volab/IoT_EPS/_1_userDoc/source/volabid.rst

:Auteur: J.Soranzo
:Societe: `VoRoBoTics`_
:Entity: `VoLAB`_

.. _`VoLAB` : http://www.vorobotics.com/wp/

.. _`VoRoBoTics` : http://www.vorobotics.com/wp/
