volab/IoT_EPS/_1_userDoc/source/chronogram.rst

++++++++++++++++++++++++++++++++++++++++++++++++++++++++++++++++++++++++++++++++++++++++++++++++++++
IoTEps Chronogram
++++++++++++++++++++++++++++++++++++++++++++++++++++++++++++++++++++++++++++++++++++++++++++++++++++

:Auteur: J.Soranzo
:Date de création: 08/2021
:Last update: 08/2021
:Societe: VoRoBoTics
:Entity: VoLAB

.. contents::
    :backlinks: top

====================================================================================================
Oscilloscope readings: loop cycle study
====================================================================================================
This timing chronogram was made with a **special version of the firmaware** that use PB0(D6) of
the ESP8266 input redefined as output. 

Shortest loop cycle
----------------------------------------------------------------------------------------------------
  
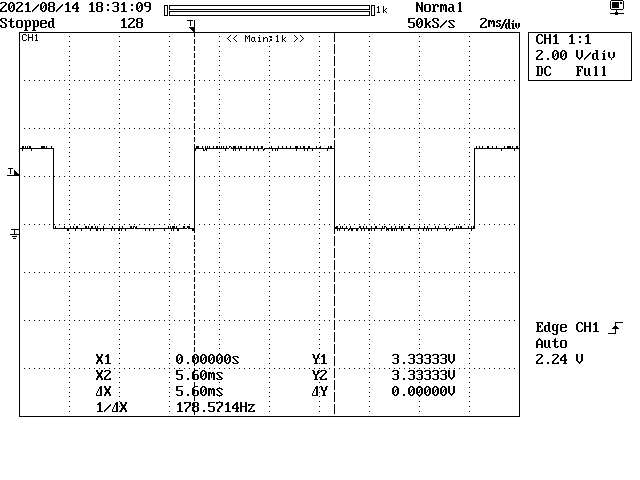
[picture p35: _1_userDoc/source/image/bestCycleTime5ms.JPG]


    Shortest loop cycle

The shortest loop cycle in idle stade is 5.6ms

A strange cycle
----------------------------------------------------------------------------------------------------

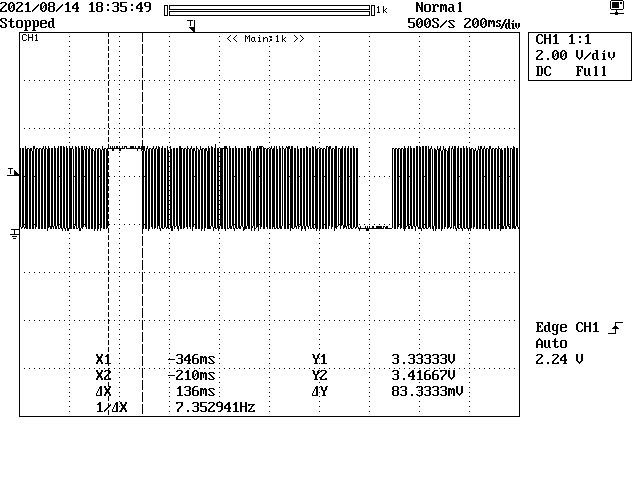
[picture p36: _1_userDoc/source/image/136msCycleEvery1s.JPG]


    136ms cycle every 1s
    
Probably web server check. Plug is in idle state (nothing to do). No 1s period timer in our code.

Push button cycle
----------------------------------------------------------------------------------------------------

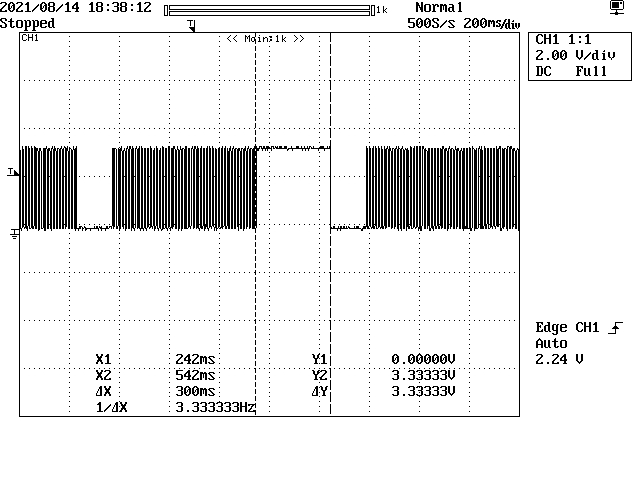
[picture p37: _1_userDoc/source/image/pushButon300msCycle.JPG]


    Handle a plug psuh button 

This operation take 300ms.

Plug on/off handler duration
----------------------------------------------------------------------------------------------------

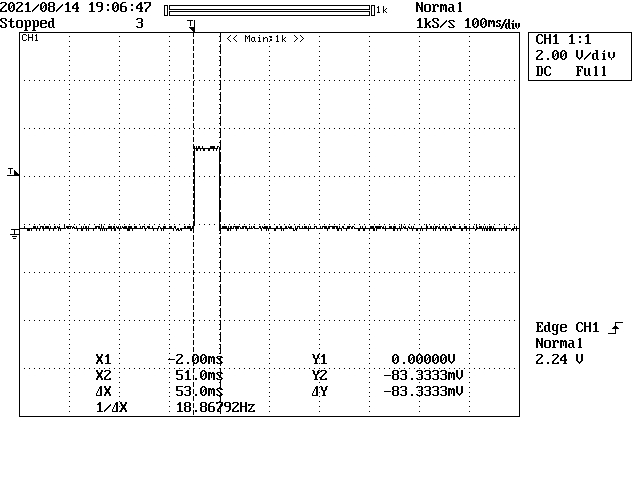
[picture p38: _1_userDoc/source/image/plugOnOff_53ms.JPG]


    Plug on/off handler take 53ms
    
and

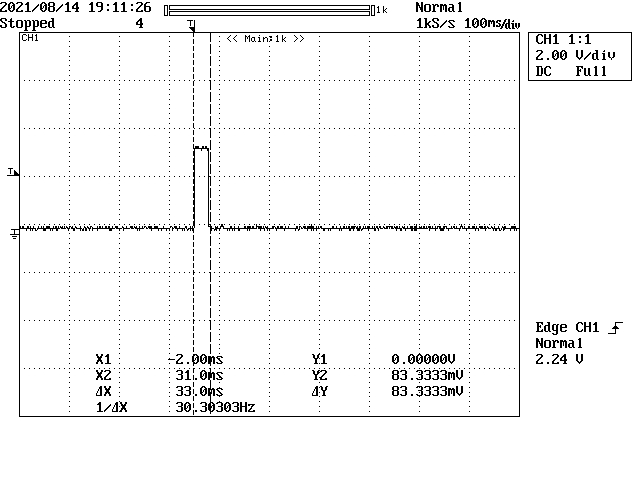
[picture p39: _1_userDoc/source/image/plugOnOff_33ms_withoutDebugPrints.JPG]


    Plug on off without debug prints 

Without debug prints on serial it take only 33ms.

A complete web exchange
----------------------------------------------------------------------------------------------------

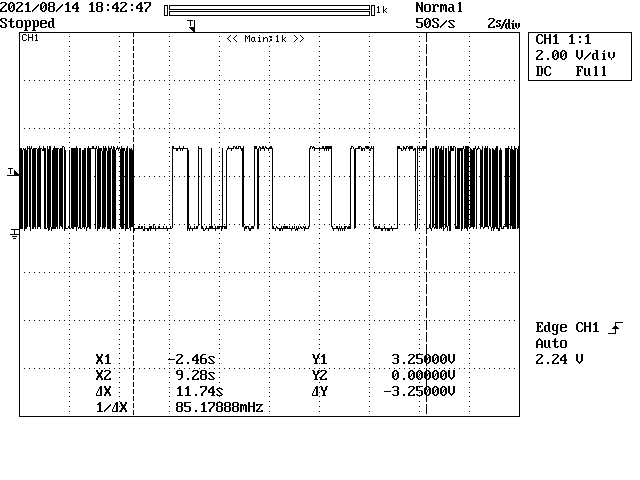
[picture p40: _1_userDoc/source/image/completeWebExchange.JPG]


    Complete web exchange : 11.74s (very long)

That correspond to::

    <Volab handleIndex > Mode Station index page
    handleFileRead: /
    handleFileRead _path : /index.html (48ko)
    handleFileRead _path : /css/sidebar.css (2ko)
    handleFileRead _path : /css/style.css (4ko)
    handleFileRead _path : /js/myLog.js (1k)
    handleFileRead _path : /js/regExPatern.js (9k)
    handleFileRead _path : /js/plug.js (19k)
    handleFileRead _path : /js/main.js (14k)
    handleFileRead _path : /js/table.js (9k)
    handleFileRead _path : /img/green.png (28k)
    handleFileRead _path : /img/logo_alpha.png (83k)
    handleFileRead _path : /img/red.png (28k)
    handleFileRead _path : /img/blue.png (28k)
    handleFileRead _path : /img/yellow.png (30k)
    handleFileRead _path : /config4.json (1.7k)

Only the function handlehtmlReq (tag pin toggle move in the function)

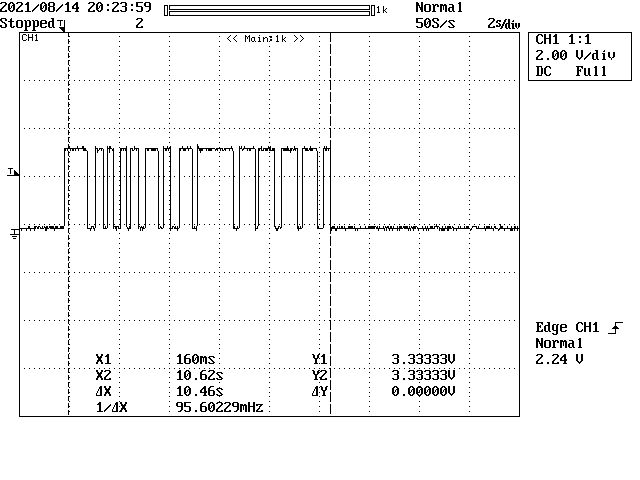
[picture p41: _1_userDoc/source/image/handleHtmlReqSlash.JPG]


    Juste time of the function 

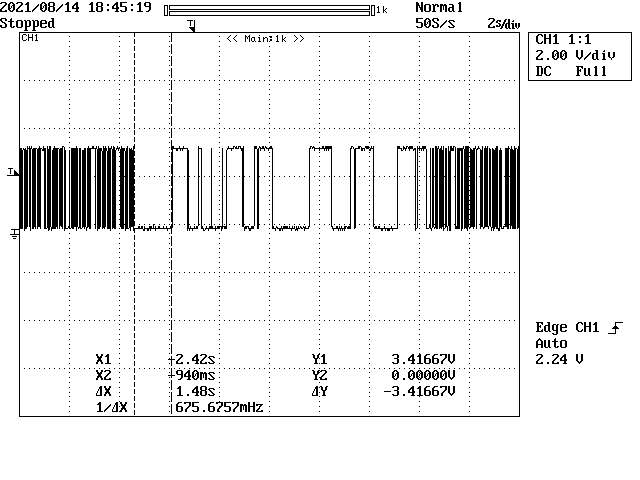
[picture p42: _1_userDoc/source/image/veryLongCycle1.48s.JPG]


    1.48s cyle

Probably the transfert of index.html

Handel html param in manual mode - example
----------------------------------------------------------------------------------------------------

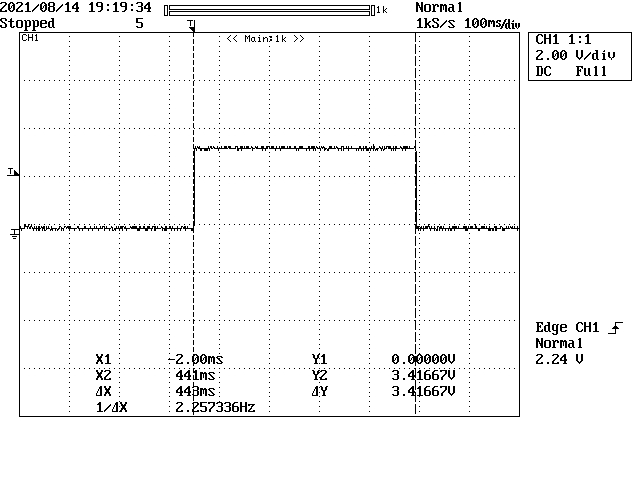
[picture p43: _1_userDoc/source/image/handleHtmlParamManualMode443ms.JPG]


    Web browser set one plug manual mode on or off
    
This operation take 443ms

====================================================================================================
Conclusions
====================================================================================================
Serial prints takes time !

The size of the files should be shorten (logo, green.png, yellow.png... javascript files)
