volab/IoT_EPS/_1_userDoc/source/pitch.rst

.. index::
    single: Pitch

++++++++++++++++++++++++++++++++++++++++++++++++++++++++++++++++
IOT Electrical Power strip from VoLAB
++++++++++++++++++++++++++++++++++++++++++++++++++++++++++++++++

.. contents:: Table of Contents
    :backlinks: top

====================
Pitcher
====================

Séléectionner ses susjets

Les tiroirs : indispensables et secondaire

CONVAINCRE

Qu'est'est-ce que je fais là ?

Qu'est-ce qu'ils font là ?

Gagner quoi ?

Se connecter à son auditoire

pas de jargon pas d'acronyme, visualisable

La lecture du non-verbal

====================
Winning Pitch
====================

Why 
----------------------------------------------------------------------------------------------------
#. aspirationnel
#. quantitatif

What
----------------------------------------------------------------------------------------------------
#. what extérieur : nom du projet, ce qu'il fait ou va faire
#. what intérieur : proposition de b=valeur innovante

Attention à la définition de innovant ne veut pas dire nouveau

Who
----------------------------------------------------------------------------------------------------
#. Par qui est porté
#. pour qui

Ci-dessus : le Warm-up pour créer l'envie

Projection pour créer l'adhésion
----------------------------------------------------------------------------------------------------

Projeter son auditoire dans l'utilisation du projet (vendre du rêve)

====================
IoT EPS
====================

Prise multiple connectée

Pourquoi ? : besoins

Cycle de croissance des plantes

Gestion de l'éclairage jour/nuit d'un aquarium

Simple minuteur

Gestion de l'éclairage quand on est en vacance

Arroser les plantes périodiqement

Pourquoi quantitatif

objectif moins de 50€

10A / prise soit 2400W avec un limite totale cumulée de 3840W

Fabricable par n'importe qui en moins de 3 heures

Quoi
 
IoT EPS Electrical Power Plug

Prise multiple connecté 4 voies avec minuteur incorporé
et mesure individuelle de puissance  pour chaque voie

Projet DiY, connecté (en Wifi)

pas d'application dédiée.

Accessible par navigateur internet

Point d'accès ou mode client Wifi

Qui

Porté par le VoLAB fabLab de Vauréal

Réalisable par tous.

Sources (électroniques, logiciels et mécaniques) disponibles sur le site internet

Se projecter

Accessible à tous.

Simple d'utilisation

Bouton mécanique pour garder la main
