volab/IoT_EPS/_1_userDoc/infography/01_Screen.jpg

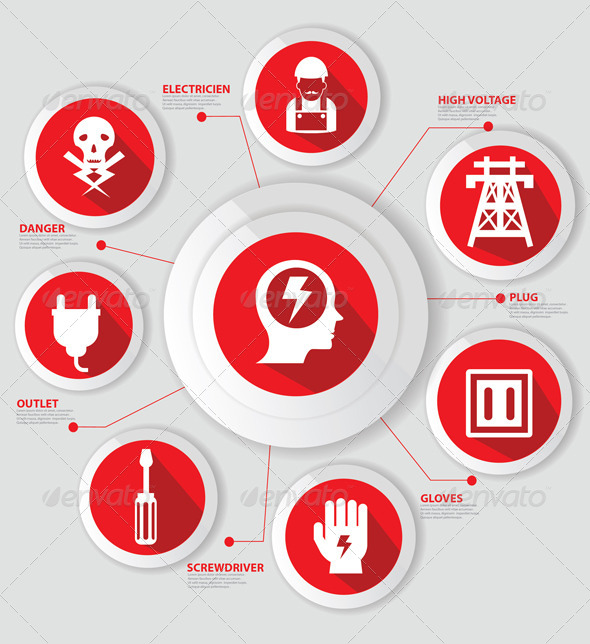
_1_userDoc/infography/01_Screen.jpg
