volab/IoT_EPS/_1_userDoc/infography/il_794xN.2478645642_a8mu.webp

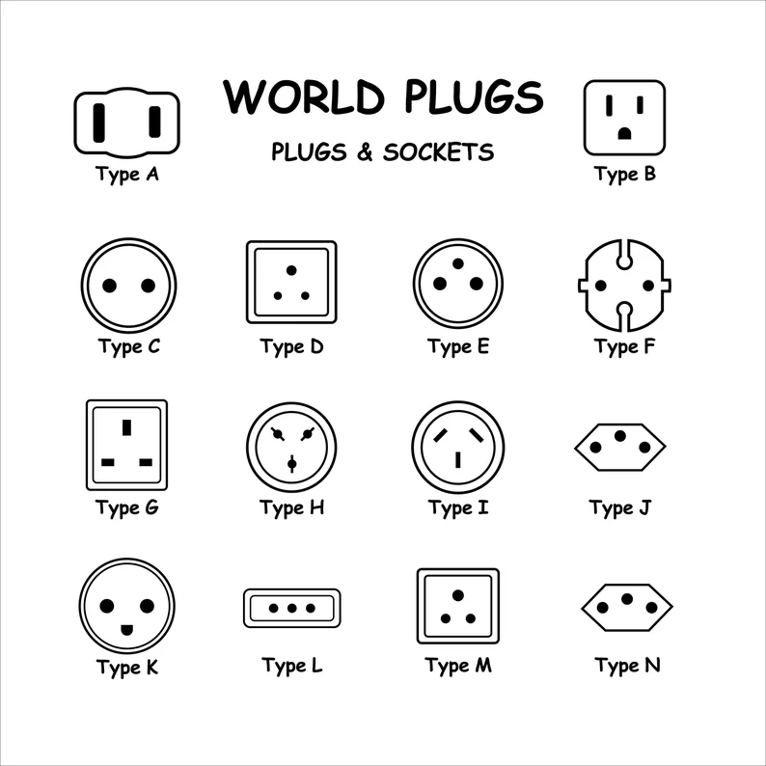
_1_userDoc/infography/il_794xN.2478645642_a8mu.webp
