volab/IoT_EPS/_1_userDoc/source/image/ACS712goodModul.jpg

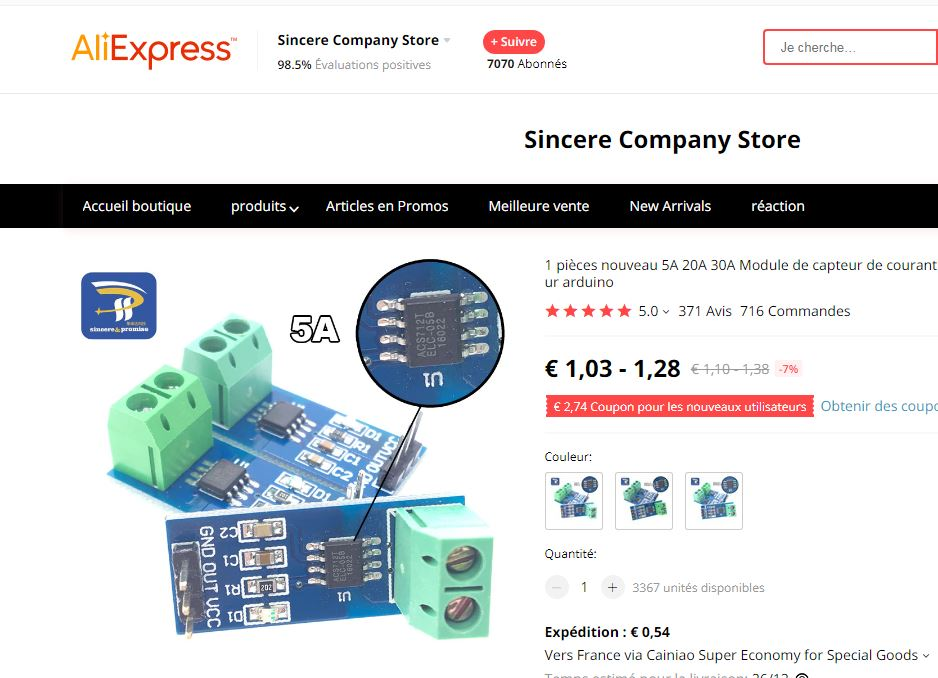
_1_userDoc/source/image/ACS712goodModul.jpg
