volab/IoT_EPS/_1_userDoc/source/image/TPLink_20200208_150122.jpg

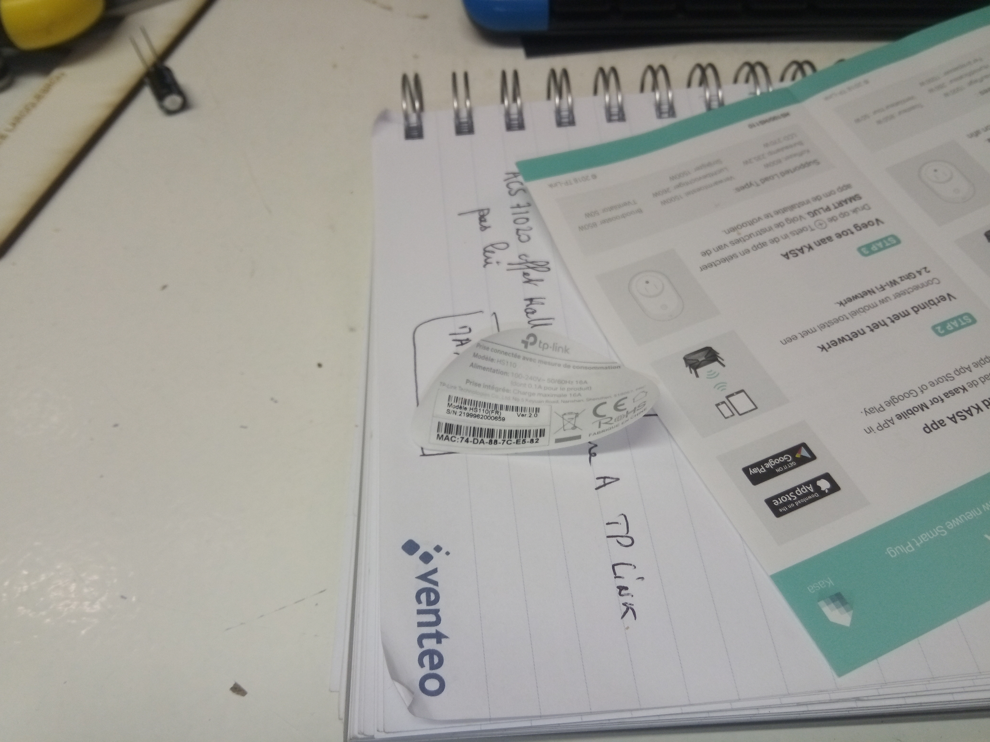
_1_userDoc/source/image/TPLink_20200208_150122.jpg
