volab/IoT_EPS/_3_software/IoT_EPS/data/img/blue.png

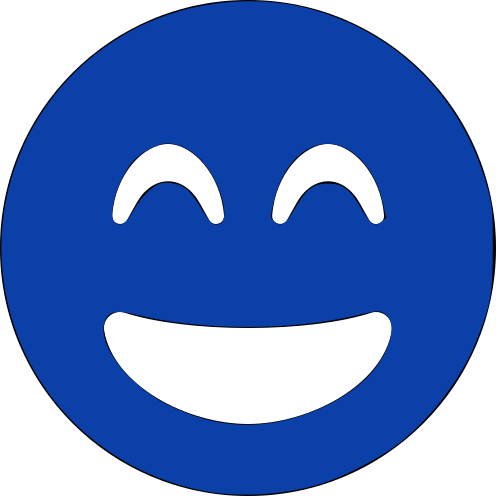
_3_software/IoT_EPS/data/img/blue.png
