volab/IoT_EPS/_3_software/IoT_EPS/data/img/yellow.png

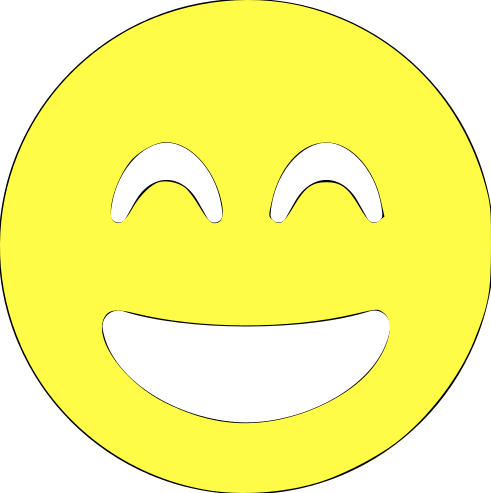
_3_software/IoT_EPS/data/img/yellow.png
