volab/IoT_EPS/_3_software/pythonTools/images/guiCalMag.JPG

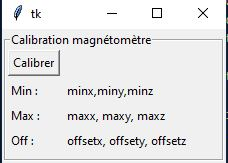
_3_software/pythonTools/images/guiCalMag.JPG
