volab/IoT_EPS/_3_software/pythonTools/images/guiDisplays.JPG

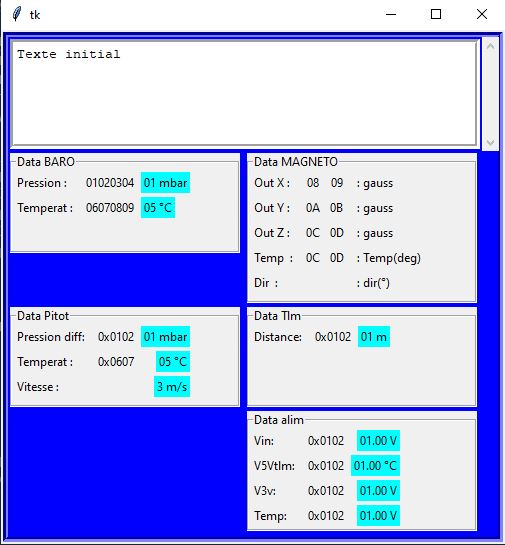
_3_software/pythonTools/images/guiDisplays.JPG
