volab/IoT_EPS/_3_software/pythonTools/images/guiRecord.JPG

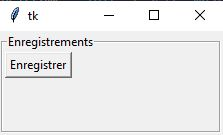
_3_software/pythonTools/images/guiRecord.JPG
