volab/IoT_EPS/_3_software/pythonTools/pytemplt/doc/images/ihm.jpg

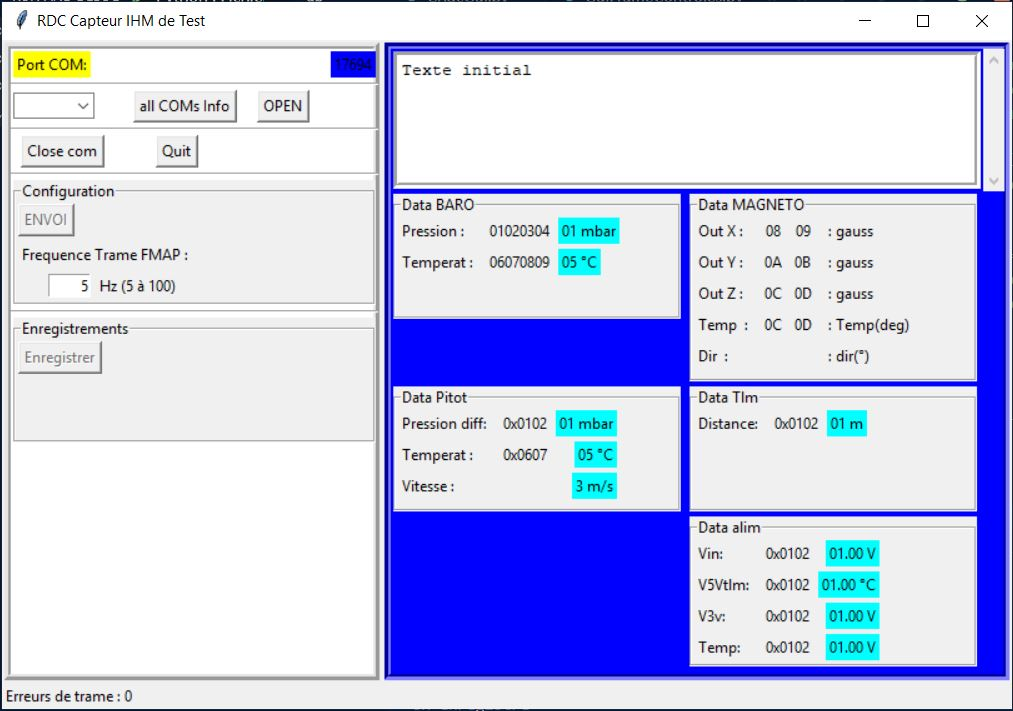
_3_software/pythonTools/pytemplt/doc/images/ihm.jpg
