volab/IoT_EPS/_1_userDoc/infography/ultimate-guide-to-travel-plugs.jpg

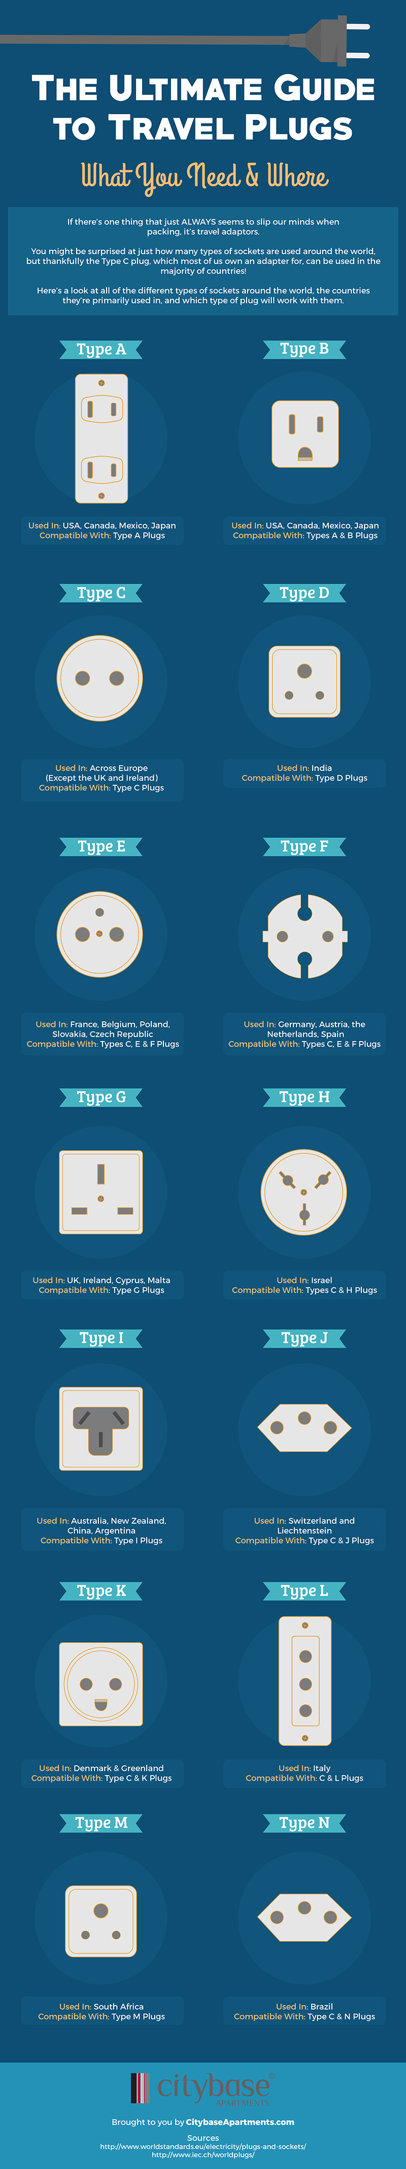
_1_userDoc/infography/ultimate-guide-to-travel-plugs.jpg
