volab/IoT_EPS/_4_PCB/IOTESP_PowerPlug_v1/IOTESP_PowerPlugv1.sch

## KiCad design _4_PCB/IOTESP_PowerPlug_v1/IOTESP_PowerPlugv1.sch (2019-04-12)

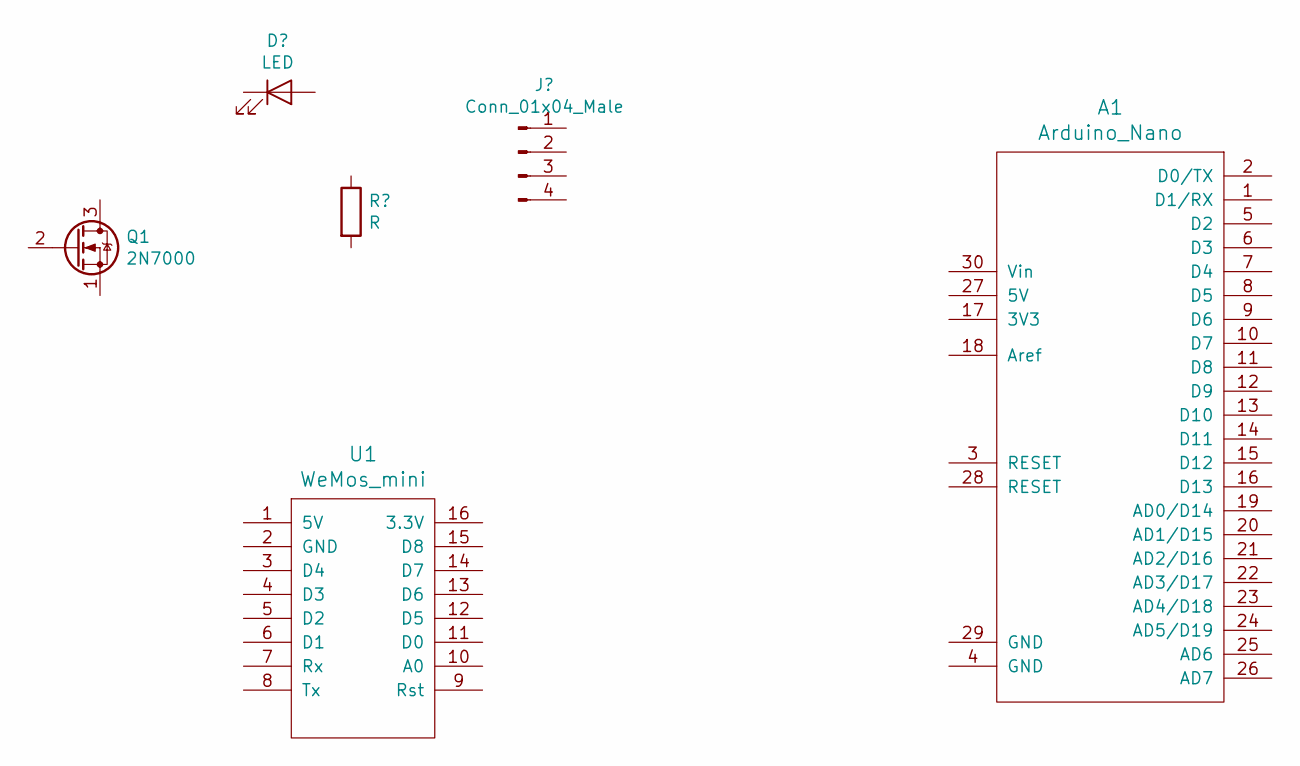
[picture p84: schematic IOTESP_PowerPlugv1.sch]

Parts:
A1: Arduino_Nano; arduino_nano
Q1: 2N7000; TO-92_Inline_Narrow_Oval
U1: WeMos_mini; D1_mini_board
