volab/IoT_EPS/_3_software/IoT_EPS/jsonIotEps.cpp

/**
* @file cpowerplug.cpp
* @author J.Soranzo
* @date 10/11/2018
* @copyright see project readme 
* @version 1.0
* @brief This class is the plug class for Electrical Power Strip project
*/

#include "jsonIotEps.h"

bool CJsonIotEps::init( ConfigParam *pcParam, CPowerPlug *plugs){
    _pcParam = pcParam;
    _pPlugs = plugs;
    return true;
}


/**
 @fn bool CJsonIotEps::checkIfStoreNeeded()
 @brief Check if CParam or CPowerPlugs store json file is needed
 @return true if store is needed
*/
bool CJsonIotEps::checkIfStoreNeeded(){
    bool retVal = false;
    DEFDPROMPT("JsonIotEps");
    
    if ( _pcParam->_jsonWriteRequest ){
        retVal=true;
    } else { //if true no need to test plug causeonly one json file
        for (int i = 0; i < _pcParam->getNumberOfPlugs(); i++ ){
            retVal |= _pPlugs[i]._jsonWriteRequest;
            //_pPlugs[i]._jsonWriteRequest = false; //to be remove after test
        }
    }

    return retVal;
}



/**
 @fn void CJsonIotEps::printFileIntegrity()
 @brief Print file integrity for debug purpose
 @return no param and no return
*/
void CJsonIotEps::printFileIntegrity(){
    DEFDPROMPT("Json file integrity print function");

    switch (_jsonFileIntegrity){
        case KEEP_MASTER:
            DSPL( dPrompt + F("Keep master"));
            //_fileNameToLoad = CONFIGFILENAME;
            break;
        case KEEP_COPY1:
            DSPL( dPrompt + F("Keep copy 1"));
            //_fileNameToLoad = CONFIGFILENAME_COPY1;
            break;  
        case KEEP_COPY2:
            DSPL( dPrompt + F("Keep copy 1"));
            //_fileNameToLoad = CONFIGFILENAME;
            break;
        case FILES_ERROR:
            DSPL( dPrompt + F("Fatal file error"));
            //_fileNameToLoad = "";
            break;           
        default:
            break;
    }
}

bool CJsonIotEps::storeJson(){
    DEFDPROMPT( "CJsonIotEps store json method" );
    DSPL( dPrompt + F("*********JSON WRITE REQUESTED***************"));
    bool retVal = false;
    

//What is the logic ?
//What is the one that this the more efficient ?
// 3 succesives writes
// followed by 3 checks and if there is error we restart x times

//from softdev.rst REX:
//Finally we decide to write only 2 files and keep the third as a template to restaure a default
//situation if the 2 others files are corrupts. This Third file is only writes when the user
//change the configuration.

//try to write conf1: _checkJsonOneFileIntegrity file1
// if ok : 
    // first write
    DSPL( dPrompt + F("Master json file write") );
    if ( _checkJsonOneFileIntegrity( CONFIGFILENAME ) ){
        _storeOneJsonFile( CONFIGFILENAME, CONFIGFILENAME );
        DSPL( dPrompt + F("store master config file with himself as model"));
        retVal = true;
    } else if ( _checkJsonOneFileIntegrity( CONFIGFILENAME_COPY1 )) {
        _storeOneJsonFile( CONFIGFILENAME_COPY1, CONFIGFILENAME );
        DSPL( dPrompt + F("store master config file with copy1 as model"));
        /** @todo [NECESSARY] rise error write config file 1 */
        retVal = true;
    } else if ( _checkJsonOneFileIntegrity( CONFIGFILENAME_COPY2 )) {
        _storeOneJsonFile( CONFIGFILENAME_COPY2, CONFIGFILENAME );
        DSPL( dPrompt + F("store master config file with copy2 as model"));
        /** @todo [NECESSARY] rise error write config file 1 with rescue values*/
        retVal = true; // or false ??? the plugs value maybe not up todate
    } else {
        /** @todo [NECESSARY] rise fatal error write config file 1 */
    }

    //second write
    DSPL( dPrompt + F("Copy 1 Json file write") );
    if ( _checkJsonOneFileIntegrity( CONFIGFILENAME ) ){
        _storeOneJsonFile( CONFIGFILENAME, CONFIGFILENAME_COPY1 );
        DSPL( dPrompt + F("store config file copy 1 with master as model"));
    } else if ( _checkJsonOneFileIntegrity( CONFIGFILENAME_COPY1 )) {
        _storeOneJsonFile( CONFIGFILENAME_COPY1, CONFIGFILENAME_COPY1 );
        DSPL( dPrompt + F("store config file copy 1 with himself as model"));
        //not an error
    } else if ( _checkJsonOneFileIntegrity( CONFIGFILENAME_COPY2 )) {
        _storeOneJsonFile( CONFIGFILENAME_COPY2, CONFIGFILENAME_COPY1 );
        DSPL( dPrompt + F("store config file copy 1 with copy 2 as model"));
    } else {
        /** @todo [NECESSARY] rise low error write config file 2 */
    }

    //third write only when config paramters has changed
    if ( _pcParam->_jsonWriteRequest ){
        if ( _checkJsonOneFileIntegrity( CONFIGFILENAME ) ){
            _storeOneJsonFile( CONFIGFILENAME, CONFIGFILENAME_COPY2 );
            DSPL( dPrompt + F("store config file copy 2 with master as model"));
        } else if ( _checkJsonOneFileIntegrity( CONFIGFILENAME_COPY1 )) {
            _storeOneJsonFile( CONFIGFILENAME_COPY1, CONFIGFILENAME_COPY2 );
            DSPL( dPrompt + F("store config file copy 2 with copy 1 as model"));
            //not an error
        } else if ( _checkJsonOneFileIntegrity( CONFIGFILENAME_COPY2 )) {
            _storeOneJsonFile( CONFIGFILENAME_COPY2, CONFIGFILENAME_COPY2 );
            DSPL( dPrompt + F("store config file copy 2 with himself as model"));
        } else {
            /** @todo [NECESSARY] rise low error write config file 3 */
        }
    }

    //clear json write request
    if ( retVal ){
        _pcParam->_jsonWriteRequest = false;
        for (int i = 0; i < _pcParam->getNumberOfPlugs(); i++ ){
            _pPlugs[i]._jsonWriteRequest = false;
        }
        _retryStoreCpt = 0;
    } else if (_retryStoreCpt < 4 ){ // next retry at next main loop
        _retryStoreCpt++;
    } else {
        /** @todo rise fatal error 3 retry on store config files */
    }

    return retVal;
}

void CJsonIotEps::_storeOneJsonFile(String file_name_model, String file_name_to_store){

    DEFDPROMPT( "CJsonIotEps store one json method" );

    File configFile = SPIFFS.open( file_name_model , "r");
    DSPL( dPrompt + "file = "+ file_name_to_store + " with model = " + file_name_model);
    if (configFile) {
        size_t size = configFile.size();
        // Allocate a buffer to store contents of the file.
        std::unique_ptr<char[]> buf(new char[size]);
        configFile.readBytes(buf.get(), size);
        configFile.close();
        DSPL( dPrompt + F("Config File loaded") );
        DynamicJsonBuffer jsonBuffer;
        JsonObject& json = jsonBuffer.parseObject(buf.get());
        if (json.success()) {
            DSPL( dPrompt + F("populate json general parm") );
            json["general"]["softAP_IP"] = _pcParam->_addIP.toString( );
            json["general"]["numberOfPlugs"] = String( _pcParam->_numberOfPlugs );
            json["general"]["softAP_port"] = String( _pcParam->_serverPort );
            json["general"]["startInAPMode"] = (_pcParam->_wifimode == "softAP") ? "ON":"OFF";
            if ( _pcParam->_firstBoot == ConfigParam::YES ){
                json["general"]["firstBoot"] = "ON";
            } else if( _pcParam->_firstBoot == ConfigParam::NO ){
                json["general"]["firstBoot"] = "OFF";
            } else { // ConfigParam::TRY
                json["general"]["firstBoot"] = "TRYSTA";
            }
            json["general"]["STAmaxWifiConnectionRetry"] = String( _pcParam->_STAmaxWifiConnectionRetries );
            json["general"]["hostName"] = _pcParam->_host;
            json["general"]["allLedsOnTime"] = String(_pcParam->_allLedsOnTime);
            json["general"]["ledsGlobalLuminosity"] = String( _pcParam->_ledsGlobalLuminosity );
            json["general"]["powerLedEconomyMode"] = _pcParam->_powerLedEconomyMode?"ON":"OFF";
            json["general"]["macAdd"] = String( _pcParam->_macAdd );
            json["general"]["softAP_macAdd"] = String( _pcParam->_softAPMacAdd );
            json["general"]["dhcp_mode"] = _pcParam->_DHCPMode?"ON":"OFF";
            json["general"]["staIP"] = _pcParam->_staIP.toString();
            json["general"]["staGateway"] = _pcParam->_staGateway.toString( );
            json["general"]["emplacement"] = String( _pcParam->_emplacement );
            for (int i = 0; i < _pcParam->getNumberOfPlugs(); i++ ){
                JsonObject& plug = json[_pPlugs[i].getPlugName()];
                DSPL( dPrompt + _pPlugs[i].getPlugName() + " write req = " + _pPlugs[i]._jsonWriteRequest );
                plug["nickName"] = _pPlugs[i]._nickName;
            }

            for (int i = 0; i < _pcParam->getNumberOfPlugs(); i++ ){
                if ( _pPlugs[i]._jsonWriteRequest ){
                    JsonObject& plug = json[_pPlugs[i].getPlugName()];
                    DSPL( dPrompt + F("plug to be writed : ") + _pPlugs[i].getPlugName() );
                    plug["State"] = _pPlugs[i]._state?"ON":"OFF";
                    plug[JSON_PARAMNAME_PAUSE] = _pPlugs[i]._pause?"ON":"OFF";
                    plug["Mode"] = _pPlugs[i].getStringMode();
                    plug["hDebut"] = _pPlugs[i]._hDebut.getStringVal();
                    plug["hFin"] =  _pPlugs[i]._hFin.getStringVal();
                    plug["dureeOn"] = _pPlugs[i]._dureeOn.getStringVal();
                    plug["dureeOff"] = _pPlugs[i]._dureeOff.getStringVal();
                    plug["clonedPlug"] = _pPlugs[i]._clonedPlug;
                    plug["onOffCount"] = String(_pPlugs[i]._onOffCount);
                    // plug["onOffCount"] = String(0);
                    plug[JSON_PARAMNAME_NEXTSWITCH] = String(_pPlugs[i]._nextTimeToSwitch);

                    //Special for day of week
                    JsonArray& plugJours = plug["Jours"];
                    for (int j = 0; j<7; j++){ //7 bits for 7 days
                        if ( bitRead( _pPlugs[i]._daysOnWeek, j ) ) plugJours[ j ]="ON";
                        else plugJours[ j ] = "OFF";
                        String jourEtat = plugJours[ j ];
                        DSPL(dPrompt + F("Jour : ") + String(j) + " = " + jourEtat );
                    }  
                }
            }
            configFile = SPIFFS.open( file_name_to_store , "w");
            json.printTo(configFile);

        } else {
            DEBUGPORT.println(dPrompt + F("Failed to load json config"));
            // return false;
        }
        //configFile.close();
        // return true;        
    }
}

/**
 @fn bool CJsonIotEps::loadJsonPlugParam( int plugNumber, int mainPowerSwitchState )
 @brief Check the integrity of json file
 @param plugNumber : Number of plugs in the system
 @param mainPowerSwitchState : to decide if we stat normaly or if we need to stop all plugs.
 @return a booleen true if all is ok.

 Need the integrity is checked before use it
*/
bool CJsonIotEps::loadJsonPlugParam( int plugNumber, int mainPowerSwitchState ){
    bool returnVal = false;
    String sState, sMode, sHDebut, sHFin, sDureeOn, sDureeOff;
    String sClonedPlug, sOnOffCount, sNextTime2switch, sPause;
    String sNickName;
    String sJours[7];
    bool writeReq = false;

    DEFDPROMPT( "Load Json Plugs Data");
    DSPL( dPrompt + F("Enter in the fonction. ")  );
    if ( _jsonFileIntegrity != FILES_ERROR ){
        File file = SPIFFS.open( _fileNameToLoad, "r");
        DSPL( dPrompt + F("File open ") + _fileNameToLoad );
        if (file){
            size_t size = file.size();
            std::unique_ptr<char[]> buf(new char[size]);
            file.readBytes(buf.get(), size);
            file.close();
            DynamicJsonBuffer jsonBuffer;
            JsonObject& json = jsonBuffer.parseObject(buf.get());
            if (json.success()){
                for (int i = 0; i < plugNumber; i++ ){
                    JsonObject& plug = json[_pPlugs[i].getPlugName()]; // bug on/off count 15/01/2022
                    if ( mainPowerSwitchState == 1 ){ // 1 if switch is on
                        // JsonObject& plug = json[_pPlugs[i].getPlugName()];
                        sNickName = plug["nickName"].as<String>();
                        sState = plug["State"].as<String>();
                        sPause = plug[JSON_PARAMNAME_PAUSE].as<String>();
                        sMode = plug["Mode"].as<String>();
                        sHDebut = plug["hDebut"].as<String>();
                        sHFin = plug["hFin"].as<String>();
                        sDureeOn = plug["dureeOn"].as<String>();
                        sDureeOff = plug["dureeOff"].as<String>();
                        sClonedPlug = plug["clonedPlug"].as<String>();
                        sOnOffCount = plug["onOffCount"].as<String>();
                        sNextTime2switch = plug[JSON_PARAMNAME_NEXTSWITCH].as<String>();

                        

                        DSPL( dPrompt + F("Plug name : ") + _pPlugs[i].getPlugName() );
                        DSPL( dPrompt + F("Nick name : ") + sNickName );
                        DSPL( dPrompt + F("Etat = ") + sState );
                        DSPL( dPrompt + F("Pause state = ") + sPause );
                        DSPL( dPrompt + F("Mode = ") + sMode );
                        DSPL( dPrompt + F("Start time = ") + sHDebut );
                        DSPL( dPrompt + F("End time = ") + sHFin );
                        DSPL( dPrompt + F("on duration = ") + sDureeOn );
                        DSPL( dPrompt + F("off duration = ") + sDureeOff );
                        DSPL( dPrompt + F("Cloned plug = ") + sClonedPlug );
                        DSPL( dPrompt + F("Relay on off count = ") + sOnOffCount );
                        DSPL( dPrompt + F("next time to switch = ") + sNextTime2switch );
                        /////////////////////////////////////////////////////////////////////////////
                        //    plugs member updates                                                 //
                        /////////////////////////////////////////////////////////////////////////////
                        _pPlugs[i]._nickName = sNickName;
                        _pPlugs[i]._state = (sState == "ON");
                        _pPlugs[i]._pause = ( sPause == "ON" );
                        _pPlugs[i]._mode = _pPlugs[i].modeId( sMode ); 
                        _pPlugs[i]._hDebut = CEpsStrTime( sHDebut, CEpsStrTime::HHMM);
                        _pPlugs[i]._hFin = CEpsStrTime( sHFin, CEpsStrTime::HHMM );
                        _pPlugs[i]._dureeOn = CEpsStrTime( sDureeOn, CEpsStrTime::MMM );
                        _pPlugs[i]._dureeOff = CEpsStrTime( sDureeOff, CEpsStrTime::MMM );
                        _pPlugs[i]._clonedPlug = sClonedPlug;
                        _pPlugs[i]._onOffCount = sOnOffCount.toInt();
                        _pPlugs[i]._nextTimeToSwitch = sNextTime2switch.toInt();

                        //restaure physical state of the plug
                        // 8/01/2022
                        // from CPowerPlug::readFromJson line 222
                        if ( _pPlugs[i]._state && (!_pPlugs[i]._pause) ) _pPlugs[i].on(); else _pPlugs[i].off();
                        
                        /////////////////////////////////////////////////////////////////////////////
                        //    special for days of Hebdo mode                                       //
                        /////////////////////////////////////////////////////////////////////////////
                        DSPL( dPrompt + "Jours : ");
                        JsonArray& plugJours = plug["Jours"];
                        _pPlugs[i]._daysOnWeek = 0;
                        for ( int i = 0; i < 7 ; i++ ){
                            sJours[i] = plugJours[i].as<String>();
                            // DSPL( dPrompt + "jours " + (String)i + " = " + sJours[i] );
                            if (sJours[i] == "ON"){
                                DSPL( "Jours " + (String)i + " est ON. " );
                                bitSet( _pPlugs[i]._daysOnWeek, i);
                            } else {
                                DSPL( "Jours " + (String)i + " est OFF. " );
                            } 
                        }
                        DSPL("");                        
                    } else { // main power switch is off stop all plugs
                    //plugs return to manual mode OFF state.
                        sOnOffCount = plug["onOffCount"].as<String>();
                        _pPlugs[i]._onOffCount = sOnOffCount.toInt(); // bug on/off count 15/01/2022
                        _pPlugs[i].handleBpLongClic();
                        writeReq = writeReq | _pPlugs[i]._jsonWriteRequest;
                        _pPlugs[i]._jsonWriteRequest = false;
                    }
                }
            }
            if ( writeReq ){
                storeJson();
            }
            returnVal = true;
        }

    } else {
        DSPL( dPrompt + F("Json file integrity error") );
    }


    return (returnVal);
}

/**
 @fn bool CJsonIotEps::loadJsonConfigParam()
 @brief Check the integrity of json file
 @return a booleen true if all is ok.

 Need the integrity is checked before use it
*/
bool CJsonIotEps::loadJsonConfigParam(){
    //bool _fileLoaded = false;
    DEFDPROMPT("CJson Config Param Loading")
    bool returnVal = false;

    if ( _jsonFileIntegrity != FILES_ERROR ){
        File file = SPIFFS.open( _fileNameToLoad, "r");
        if (file){
            size_t size = file.size();
            std::unique_ptr<char[]> buf(new char[size]);
            file.readBytes(buf.get(), size);
            file.close();
            DynamicJsonBuffer jsonBuffer;
            JsonObject& json = jsonBuffer.parseObject(buf.get());
            if (json.success()){
                String s_IpAdd = json["general"]["softAP_IP"].as<String>();
                _pcParam->_addIP.fromString( s_IpAdd );
                _pcParam->_numberOfPlugs = json["general"]["numberOfPlugs"].as<String>().toInt();
                _pcParam->_serverPort = json["general"]["softAP_port"].as<String>().toInt();
                String startInAPMode = json["general"]["startInAPMode"].as<String>();
                if ( startInAPMode == "OFF") _pcParam->_wifimode = "Station";
                else _pcParam->_wifimode = "softAP";
                String s_FirstBootTmp = json["general"]["firstBoot"].as<String>();
                //possible value are "ON" "OFF" or "TRYSTA"
                if ( s_FirstBootTmp == "ON") _pcParam->_firstBoot = ConfigParam::YES;
                else if ( s_FirstBootTmp == "OFF" ) _pcParam->_firstBoot = ConfigParam::NO;
                else if ( s_FirstBootTmp == "TRYSTA" ) _pcParam->_firstBoot = ConfigParam::TRY;
                else _pcParam->_firstBoot = ConfigParam::YES; // default value
                _pcParam->_STAmaxWifiConnectionRetries = \
                        json["general"]["STAmaxWifiConnectionRetry"].as<String>().toInt();
                _pcParam->_host = json["general"]["hostName"].as<String>();
                _pcParam->_allLedsOnTime = json["general"]["allLedsOnTime"].as<String>().toInt();
                _pcParam->_ledsGlobalLuminosity = \
                    json["general"]["ledsGlobalLuminosity"].as<String>().toInt();
                _pcParam->_powerLedEconomyMode = \
                        (json["general"]["powerLedEconomyMode"].as<String>() == "ON");
                _pcParam->_macAdd = json["general"]["macAdd"].as<String>();
                _pcParam->_softAPMacAdd = json["general"]["softAP_macAdd"].as<String>();
                _pcParam->_DHCPMode = ( json["general"]["dhcp_mode"].as<String>() == "ON" );
                String s_tmpIP = json["general"]["staIP"].as<String>();
                _pcParam->_staIP.fromString( s_tmpIP );
                s_tmpIP = json["general"]["staGateway"].as<String>();
                _pcParam->_staGateway.fromString( s_tmpIP );
                if (_pcParam->_firstBoot == ConfigParam::YES ) _pcParam->_wifimode = "softAP";
                _pcParam->_emplacement = json["general"]["emplacement"].as<String>();
                returnVal = true;
                /** @todo [NECESSARY] clear usage of NTP error */ 
            } else {
                DSPL(dPrompt + F("Failed to load json config"));     
                returnVal = false;
            }  
        }
        DSPL( dPrompt + F("Config param loaded : "));
        DSPL( dPrompt + F(" - emplacement : ") + _pcParam->_emplacement );
        DSPL( dPrompt + F(" - Number of plugs : ") + String(_pcParam->_numberOfPlugs) );
        DSPL( dPrompt + F(" - All Led On Time : ") + String(_pcParam->_allLedsOnTime)  );
        DSPL( dPrompt + F(" - LEDs Global illum : ") + String(_pcParam->_ledsGlobalLuminosity) );
        DSPL( dPrompt + F(" - Power Led economy mode : ") +  _pcParam->_powerLedEconomyMode );
        String firstBoot_s;
        switch (_pcParam->_firstBoot){
            case ConfigParam::YES:
                firstBoot_s = "YES";
                break;
            case ConfigParam::NO:
                firstBoot_s = "NO";
                break;
            case ConfigParam::TRY:
                firstBoot_s = "TRY";
                break;            
            default:
                break;
        }
        DSPL( dPrompt + F(" - First boot : ") +  firstBoot_s );
        DSPL( dPrompt + F(" - Host name : ") +  _pcParam->_host );
        DSPL( dPrompt + F(" - Strat in AP mode (_wifiMode) : ") + _pcParam->_wifimode  );
        DSP( dPrompt + F(" - Soft AP IP add (_addIP) : " )); _pcParam->_addIP.printTo(Serial);DSPL();
        DSPL( dPrompt + F(" - Soft AP port (_serverPort): ") + String(_pcParam->_serverPort)  );
        DSPL( dPrompt + F(" - DHCP mode  : ") + (_pcParam->_DHCPMode?"ON":"OFF")  );
        DSP( dPrompt + F(" - Station IP address  : ") );_pcParam->_staIP.printTo(Serial);DSPL();
        DSP( dPrompt + F(" - Station gateway IP address  : ") ); _pcParam->_staGateway.printTo(Serial);DSPL();
        DSPL( dPrompt + F(" - MAC address  : ") +  _pcParam->_macAdd  );
        DSPL( dPrompt + F(" - Soft AP MAC address  : ") + _pcParam->_softAPMacAdd  );
        DSPL( dPrompt + F(" - MAX Wifi connexion retry  : ") + String(_pcParam->_STAmaxWifiConnectionRetries)  );
        //DSPL( dPrompt + F(" - TNP Error  : ") +   ); //CSysSattus::ntpErr
    }
 
    return returnVal;
}

/**
 @fn CJsonIotEps::jsonFileIntegrity_t CJsonIotEps::checkJsonFilesIntegrity()
 @brief Check the integrity of json files
 @return jsonFileIntegrity Value.

 This method is called in the system init. It sets the _jsonFileIntegrity and 
 _fileNameToLoad private members.
*/
CJsonIotEps::jsonFileIntegrity_t CJsonIotEps::checkJsonFilesIntegrity(){ 
    // uint32_t H0 = 0;
    // uint32_t H1 = 0;
    // uint32_t H2 = 0;
    _jsonFileIntegrity = FILES_ERROR;

    DEFDPROMPT("Check Json Integrity")
/*
    DSPL( dPrompt +F("Mounting FS..."));
    ///SPIFFS Opning
    if (SPIFFS.begin()) {
        DSPL(dPrompt + F("File system mounted "));
        // if (SPIFFS.exists("/config.json")) {
        if (SPIFFS.exists( CONFIGFILENAME)) {
            //file exists, reading and loading
            DSPL(dPrompt + F("reading Json file master"));
            File configFile = SPIFFS.open( CONFIGFILENAME, "r");
            if (configFile) { H0 = _hashFile( configFile ); }
            DSPL(dPrompt + "H0 = " + String(H0));
        }
        if (SPIFFS.exists( CONFIGFILENAME_COPY1 )) {
            DSPL(dPrompt + F("reading Json file copy1"));
            File configFile = SPIFFS.open( CONFIGFILENAME_COPY1, "r");
            if (configFile) { H1 = _hashFile( configFile ); }
            DSPL(dPrompt + "H1 = " + String(H1));
        }
        if (SPIFFS.exists( CONFIGFILENAME_COPY2 )) {
            DSPL(dPrompt + F("reading Json file copy2"));
            File configFile = SPIFFS.open( CONFIGFILENAME_COPY2, "r");
            if (configFile) { H2 = _hashFile( configFile ); }
            DSPL(dPrompt + "H2 = " + String( H2 ));
        }        
    }

    if ( H0 !=0 ){
        if ( H0 == H1 ){ _jsonFileIntegrity = KEEP_MASTER; }//best situation
        else if ( H0 == H2 ){ _jsonFileIntegrity = KEEP_MASTER; } //low probability
        //cause it means that copy1 corrupted and not master and copy2
        //sequence of wrtites is master, copy1 and at the end copy2
        //not only in the best situation, H0 != 0, and H0 == H1 == H2 ie H0 == H2 but this case
        //is already take into account with nested if
        else if (H1 !=0 ){//H1 could be equal to H2 if H1 and H2 are eqal to 0: H1 !=0 added
            if ( H1 == H2){ _jsonFileIntegrity = KEEP_COPY1; }
                //master H0 corrupted but !=0 never saw but... possible due to this risk keep copy
                //master good but previous write process stopped between write 0 and 1
        } else { //H1 == 0
            _jsonFileIntegrity = TRY_MASTER;
        }

        
    }

    //if (H0, H1 and H2 !=0) and H0 != H1 != H2 (all hash values are differents)
    //this situation corresponds to a good master write but wrong write at the time of first copy
    //In this case master is good and has a hash value, copy1 is wrong and has a diffrent hash value
    //regardless of master and copy2 and copy2 is good but is out of date and has a third hash value
    if ( H0 != H1 && H0 != H2 && H1 != H2 ){  }
    // could be KEEP_MASTER

    //if only H0 != 0 we can try to use it
    if (H0 !=0 && H1 == 0 && H2 ==0 ){ _jsonFileIntegrity = TRY_MASTER; }
    // could be KEEP_MASTER

    //If all hash value are 0 there is no file : it is a fatal error
    
    switch (_jsonFileIntegrity){
        case KEEP_MASTER:
            DSPL( dPrompt + F("Keep master"));
            _fileNameToLoad = CONFIGFILENAME;
            break;
        case KEEP_COPY1:
            DSPL( dPrompt + F("Keep copy"));
            _fileNameToLoad = CONFIGFILENAME_COPY1;
            break;  
        case TRY_MASTER:
            DSPL( dPrompt + F("Try master"));
            _fileNameToLoad = CONFIGFILENAME;
            break;
        case FILES_ERROR:
            DSPL( dPrompt + F("Fatal file error"));
            _fileNameToLoad = "";
            break;           
        default:
            break;
    }
*/
    //Check file spacial Tag Values (Version an TAG)
    if ( _checkJsonOneFileIntegrity( CONFIGFILENAME)  ){
        _fileNameToLoad = CONFIGFILENAME;
        _jsonFileIntegrity = KEEP_MASTER;
    } else if ( _checkJsonOneFileIntegrity( CONFIGFILENAME_COPY1 ) ){
        _fileNameToLoad = CONFIGFILENAME_COPY1;
        _jsonFileIntegrity = KEEP_COPY1;
    } else if ( _checkJsonOneFileIntegrity( CONFIGFILENAME_COPY2 )){
        _fileNameToLoad = CONFIGFILENAME_COPY2;
        _jsonFileIntegrity = KEEP_COPY2;
    } else {
        _fileNameToLoad = "";
        _jsonFileIntegrity = FILES_ERROR;
    }

    return _jsonFileIntegrity;
}

/**
 @fn bool CJsonIotEps::_checkJsonOneFileIntegrity( String fileName )
 @brief Check the integrity of one json file
 @param fileName The file name to check
 @return true if file is correct.

 This method is called in the system init. It sets the _jsonFileIntegrity and 
 _fileNameToLoad private members if json_version and tag are correct.
*/
bool CJsonIotEps::_checkJsonOneFileIntegrity( String fileName ){
    DEFDPROMPT("Check Json Integrity (one file)")
    bool returnVal = false;
    _jsonVersion = "";
    _jsonTag = "";
    // DSPL( dPrompt );
    File file = SPIFFS.open( fileName, "r");
    if (file){
        size_t size = file.size();
        std::unique_ptr<char[]> buf(new char[size]);
        file.readBytes(buf.get(), size);
        file.close();
        DynamicJsonBuffer jsonBuffer;
        JsonObject& json = jsonBuffer.parseObject(buf.get());
        if (json.success()) {
            _jsonVersion = json["jsonVersion"].as<String>();
            _jsonTag = json["jsonTag"].as<String>();
            DSPL( dPrompt + F("file : ") + fileName + F(", JSON file read version : ") + _jsonVersion );
        }
    }
    
    if ( ( _jsonVersion == JSON_VERSION ) && ( _jsonTag == JSON_TAG ) ){
        // _jsonFileIntegrity = FILES_ERROR;
        // _fileNameToLoad = "";
        returnVal = true;        
    } else {
        returnVal = false;
    }

    return returnVal;

}
