volab/IoT_EPS/_3_software/IoT_EPS/csystem.cpp

/**
 @file csystem.cpp
 @author J.SORANZO
 @date 30/06/2020
 @copyright 2020 CC0
 @version git versionning
 @brief Fichier d'implémentation de la classe system pour englober tout le system
*/

#include "csystem.h"
#include "config_advanced.h"

// VoLAB Logo (1kB size : 128*64 /8 - 8 bytes/line)
//generated with http://en.radzio.dxp.pl/bitmap_converter/
//parameters : Horizontal little endianess

const unsigned char CSystem::logoLab [1024] = {
0x00, 0x00, 0x00, 0x00, 0x00, 0x00, 0x00, 0x00, 0x00, 0x00, 0x00, 0x00, 0x00, 0x00, 0x00, 0x00,
0x00, 0x00, 0x00, 0x00, 0x00, 0x00, 0x00, 0x00, 0x00, 0x00, 0x00, 0x00, 0x00, 0x00, 0x00, 0x00,
0x00, 0x00, 0x00, 0x1F, 0xC0, 0x00, 0x00, 0x00, 0x00, 0x00, 0x00, 0x00, 0x00, 0x00, 0x00, 0x00,
0x00, 0x00, 0x00, 0x60, 0x60, 0x00, 0x00, 0x00, 0x00, 0x00, 0x00, 0x00, 0x00, 0x00, 0x00, 0x00,
0x00, 0x00, 0x00, 0xCF, 0x10, 0x00, 0x00, 0x00, 0x00, 0x00, 0x00, 0x00, 0x00, 0x00, 0x00, 0x00,
0x00, 0x00, 0x00, 0x9F, 0xD8, 0x00, 0x00, 0x00, 0x00, 0x00, 0x00, 0x00, 0x00, 0x07, 0xFF, 0xE0,
0x00, 0x00, 0x01, 0xB9, 0xC8, 0x00, 0x00, 0x00, 0x0F, 0xC0, 0x00, 0x00, 0x00, 0x1F, 0xFF, 0xF8,
0x00, 0x00, 0x01, 0x70, 0xE8, 0x00, 0x00, 0x00, 0x18, 0x60, 0x00, 0x00, 0x00, 0x30, 0x00, 0x1C,
0x00, 0x00, 0x01, 0x66, 0x68, 0x00, 0x00, 0x00, 0x20, 0x10, 0x00, 0x00, 0x00, 0x60, 0x00, 0x0E,
0x00, 0x00, 0x01, 0x66, 0x68, 0x00, 0x00, 0x00, 0x23, 0x10, 0x00, 0x00, 0x00, 0x60, 0x00, 0x06,
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
0x20, 0x00, 0x00, 0x00, 0x00, 0x22, 0xF9, 0xCF, 0xA2, 0x70, 0x00, 0x00, 0x00, 0x00, 0x00, 0x02,
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
};



void CSystem::oledLoopBackScreen(){
    _pDisplay->setCursor(0,0);
    _pDisplay->drawBitmap(0,0, loopBackScreen, 128,64,1);
    // _pDisplay->display();   
}


void CSystem::oledDisplayDate(){
    
    //String date;
    char date[21];
    _pDisplay->setCursor( OLED_XPOS_STARTLIGN, OLED_YPOS_FOR_DATE);
    DateTime now = _rtc.now();
    
    // date = (String)now.day()+"/"+(String)now.month()+"/";
    // date += (String)now.year()+"   ";
    // date += (String)now.hour()+":"+ (String)now.minute()+":";
    // date += (String)now.second();  
    // _oledBlankLine(OLED_XPOS_STARTLIGN, OLED_YPOS_FOR_DATE);
    sprintf( date, "%02d/%02d/%04d  %02d:%02d:%02d", now.day(), now.month(), now.year(), now.hour(), 
    now.minute(), now.second());
  
    _pDisplay->println(date);
    // _pDisplay->display(); 
}
void CSystem::oledDisplaySate(){
    // _oledBlankLine(OLED_XPOS_STARTLIGN, OLED_YPOS_FOR_STATE); 
    _pDisplay->setCursor(OLED_XPOS_STARTLIGN, OLED_YPOS_FOR_STATE);
    String message;
    DEFDPROMPT( "CSystem::oledDisplatState" )
    // if ( _psysStat->isSystemok() ){
        // display one plug state
        // message = _pPlugs[_oledCptPlugToDisplay].getPlugName();
        // message += " mode ";
        // message += (String)_pPlugs[_oledCptPlugToDisplay++].getMode();

    message = "Mode ";
    message += (String)_pPlugs[_oledCptPlugToDisplay].getMode();
    message += " : ";
    message += _pPlugs[_oledCptPlugToDisplay].getPlugName();

    _oledDivSysState--; //to slow down the display speed
    if ( _oledDivSysState == 0 ){
        _oledDivSysState = (uint8_t)OLED_SYSTEM_STATE_DISPLAY_DIV;
        _oledCptPlugToDisplay++;
    }

    if ( _oledCptPlugToDisplay >= _pcParam->getNumberOfPlugs() ){
        _oledCptPlugToDisplay = 0;
    }

    _pDisplay->println(message);   
}

void CSystem::oledDisplayIps(){
    // _oledBlankLine(OLED_XPOS_STARTLIGN, OLED_YPOS_FOR_LAN_IPADD);
    _pDisplay->setCursor(OLED_XPOS_STARTLIGN, OLED_YPOS_FOR_LAN_IPADD);
    _pDisplay->println("LAN:" + WiFi.localIP().toString() );
    // _oledBlankLine(OLED_XPOS_STARTLIGN, OLED_YPOS_FOR_AP_IPADD);
    _pDisplay->setCursor(OLED_XPOS_STARTLIGN, OLED_YPOS_FOR_AP_IPADD);
    // if ( !_psysStat->wifiSoftApErr.isErr() ){
    if ( _psysStat->isSystemok() ){
        _pDisplay->println(" AP:" + WiFi.softAPIP().toString() );
    } else {
        // _pDisplay->println(" AP:error" );
        if ( _oledCptErrToDisplay == 0 ) _oledCptErrToDisplay = _psysStat->howManyError();
        _pDisplay->println( _psysStat->getMsg( _oledCptErrToDisplay-- ) );
    }
   
     
}

void CSystem::oledLoopChangeDispayIf(){
    DEFDPROMPT( "CSystem::oledLoopChangeDispayIf" )
    if ( millis() - _oledPrevMillis > _oledRefreshPeriod*1000 ){
        _oledPrevMillis = millis();
        _pDisplay->clearDisplay();

        oledLoopBackScreen();  
        
        oledDisplayDate();
        oledDisplayIps();
        //do the job here

        oledDisplaySate();
        

        _pDisplay->display();
    
        
    }   
}

void CSystem::oledDsiplayShutDown(){
    _pDisplay->clearDisplay();
    _pDisplay->println( F(OLED_SHUTDOWN_MESSAGE) );
    _pDisplay->display();
}


/**
 @fn void CSystem::init( WiFiUDP &ntpUDP, CSysStatus *psysStat, FS *pFileSyst, ConfigParam *pcParam,
                    const String *necessaryFileList, int necessaryFileNbr, String buildinfo
                    , ESP8266WiFiClass *pWifi, CNanoI2CIOExpander *pNanoioExp
                    , Adafruit_SSD1306 *pdisplay )
 @brief IoT_EPS system init method
 @param ntpUDP just for NTPClient init, this parameter is not kept
 @param psysStat a pointer on global variable sysStatus
 @param pFileSyst a pointer on the file system
 @param pcParam a pointer on the cParm class instance
 @param necessaryFileList a pointer on the necessary list files
 @param necessaryFileNbr a many necessary files
 @param buildInfo as ti says
 @param pWifi a pointer on the wifi class connection
 @param pNanoioExp a pointer on the instance of nano io expension
 @param pdisplay a pointer on the oled display
 @param pjsonData a ref to jsonData
 @return no return val

Start RTc DS3231 and nothing else @25/09/2020. With all this pointers Csysteminstance can inteeract
with almost all components in the system.
*/
void CSystem::init( WiFiUDP &ntpUDP, CSysStatus *psysStat, FS *pFileSyst, ConfigParam *pcParam,
                    const String *necessaryFileList, int necessaryFileNbr, String buildInfo
                    , ESP8266WiFiClass *pWifi, CNanoI2CIOExpander *pNanoioExp
                    , Adafruit_SSD1306 *pdisplay
                    , CJsonIotEps *pjsonData
                     ){

    DEFDPROMPT( "CSystem::init" )

    String message;
    String date;

    _psysStat = psysStat;
    _pFileSystem = pFileSyst;
    _pcParam = pcParam;
    _pNecessaryFiles = necessaryFileList;
    _pDisplay = pdisplay;
    _pJsonData = pjsonData;
    _pJsonData->init( _pcParam, _pPlugs );

    

    
    delay(1000);//a try to correct the powerup pb
    pinMode(LED_BUILTIN, OUTPUT);
    digitalWrite( LED_BUILTIN, LOW ); //warning D4 BP bleue plug
    delay(1000);
    digitalWrite( LED_BUILTIN, HIGH ); //warning D4 BP bleue plug
    pinMode(LED_BUILTIN, INPUT);

    DSPL();
    DSPL( dPrompt + F("Sketch start..."));
    pinMode( BP1, INPUT_PULLUP );

    /////////////////////////////////////////////////////////////////////////////
    //     file system check                                                   //
    /////////////////////////////////////////////////////////////////////////////
    DSPL( dPrompt + " Build : " + buildInfo );
    _psysStat->fsErr.err( !_pFileSystem->begin() ); 
    DSPL( dPrompt + F("File system correctly Open @ setup level") );

    /////////////////////////////////////////////////////////////////////////////
    //     Special Actions                                                     //
    /////////////////////////////////////////////////////////////////////////////
    if ( !(digitalRead(BP1) ) ){ // green PB
        DSPL( dPrompt + F("Special action take place..." ) );
        // place special actions here
        // example sysStatus._forceSystemStartOnFatalError = true;
        /** @todo [NECESSARY] creatDefaultJson with new class jsonIoTEps */
        _pcParam->creatDefaultJson();
    }

    /////////////////////////////////////////////////////////////////////////////
    //  Start of the check necessary files  presence                           //
    /////////////////////////////////////////////////////////////////////////////
    DSPL(dPrompt + F("File check !") );
    bool fileExist = true;
    for ( int i = 0; i < necessaryFileNbr; i++){
        String s = necessaryFileList[i];
        bool b = _pFileSystem->exists(s);
        fileExist &= b;
        DSPL( dPrompt + F("file : ") + s + F(" is ") + (b?F("present"):F("not found")) );
    }
    DSPL( dPrompt + F("Result all files are present ? ") + (fileExist?"OK":"ERROR") );
    _psysStat->filesErr.err( !fileExist );

    _pJsonData->checkJsonFilesIntegrity();
    /////////////////////////////////////////////////////////////////////////////
    //     Config param check                                                  //
    /////////////////////////////////////////////////////////////////////////////

    _pcParam->begin();
    _pcParam->ready = _pJsonData->loadJsonConfigParam();
    _psysStat->confFileErr.err( !_pcParam->ready );
    DSPL( dPrompt + F("json mac add : ") + _pcParam->getMacAdd() );
    DSPL( dPrompt + F("Board Sation MAC add = ") + pWifi->macAddress() );
    if ( _pcParam->getMacAdd() == pWifi->macAddress() ) DSPL( dPrompt + "Station equal add");
    else {
        DSPL( dPrompt + "diff add, write to json");
        _pcParam->write2Json( "macAdd", pWifi->macAddress() );
    }
    DSPL( dPrompt + F("json Soft AP mac add : ") + _pcParam->getSoftAPMacAdd() );
    DSPL( dPrompt + F("Board Soft AP MAC add = ") + pWifi->softAPmacAddress() );
    if ( _pcParam->getSoftAPMacAdd() == pWifi->softAPmacAddress() ) DSPL( dPrompt + "AP equal add");
    else {
        DSPL( dPrompt + "diff add, write to json");
        _pcParam->write2Json( "softAP_macAdd", pWifi->softAPmacAddress() );
    }
    /////////////////////////////////////////////////////////////////////////////
    //     I2C bus check                                                       //
    ///////////////////////////////////////////////////////////////////////////// 
    CNano::init();
    DSPL( dPrompt+ F("I2C test start") );
    int cpt = 1;
    do{
        if ( !pNanoioExp->test() ){
            DSPL( dPrompt + "i2cRecov" + " number " + cpt);
            SerialCommand::i2c_recovery();
        } else cpt = 9;
        
        cpt++;
    } while (cpt < I2C_RETRIES );
    if (cpt != 10) _psysStat->nanoErr.err( true );
    DSPL(dPrompt + F("Nano test ok"));

    /////////////////////////////////////////////////////////////////////////////
    //     OLED Start message                                                    //
    /////////////////////////////////////////////////////////////////////////////
    DSPL(dPrompt + F("Display oled Logo"));
    _oledStartMessagesManager();



    /////////////////////////////////////////////////////////////////////////////
    //     rtc DS3231 start                                                    //
    /////////////////////////////////////////////////////////////////////////////
    
    _pTimeclient = new NTPClient(ntpUDP, NTPSERVER);
    _pTimeclient->setTimeOffset( OFFSET_HEURE * SECPERHOURS );
    _rtc.begin( _pTimeclient );
    _psysStat->rtcErr.err( _rtc.initErr );
    if (_rtc.lostPower()){
        DSPL( dPrompt + F("une remise a l'heure est necessaire") );
    }
    DateTime now = _rtc.now();
    message = dPrompt + F("DS3231 Start date : ");
    date = (String)now.day()+"/"+(String)now.month()+"/";
    date += (String)now.year()+" ";
    date += (String)now.hour()+":"+ (String)now.minute()+":";
    date += (String)now.second();  
    message += date;    
    DSPL( message);

    /////////////////////////////////////////////////////////////////////////////
    //     OLED check messages                                                 //
    /////////////////////////////////////////////////////////////////////////////    
    _pDisplay->setCursor(0,0);
    _pDisplay->println(DS3231_START_DATE);
    _pDisplay->println(date);
    _pDisplay->println();
    _pDisplay->println(AT_THIS_POINT);
    _pDisplay->println("* I2C ok"); //L5
    _pDisplay->println(OLED_FILE_SYSTEM_OK);
    _pDisplay->println(OLED_CONFIG_PARAM_OK );

    _pDisplay->display();
    delay(5000);
    _pDisplay->clearDisplay();
    _pDisplay->setCursor(0,0);
    _pDisplay->display();
    _oledRefreshPeriod = OLED_REFRESH_PERIOD;
    _oledPrevMillis = millis();                    

    _oledCptPlugToDisplay = 0;
    
        
}

void CSystem::setPlugsAdd( CPowerPlug *plugs ){ 
    _pPlugs = plugs;
    _pJsonData->init( _pcParam, _pPlugs ); 
}


/**
 @fn void CSystem::timeServerCheck()
 @brief IoT_EPS Check time server access
 @return not param and no return value

Need to be called after Wifi init cause _psysStat->ntpEnabled set by Wifi link
*/
void CSystem::timeServerCheck(){
    /////////////////////////////////////////////////////////////////////////////
    //  Time server check                                                     //
    /////////////////////////////////////////////////////////////////////////////
    // if ((wifi is on station mode connected))
    int timeZone = OFFSET_HEURE;
    DateTime NTPTime;
    DEFDPROMPT( "CSystem::timeServerCheck" )

    if( _psysStat->ntpEnabled){
        DSPL(dPrompt + F("check started") );
        _pTimeclient->begin();

        _psysStat->ntpErr.err( !_pTimeclient->forceUpdate() ) ;
        if ( !_psysStat->ntpErr.isErr() ){
            _pTimeclient->setTimeOffset( timeZone * SECPERHOURS );
            // setTime(  timeClient.getEpochTime() );
            NTPTime = DateTime( _pTimeclient->getEpochTime() );
            String sDate = "";
            sDate += (String)NTPTime.day() +"/"+(String)NTPTime.month()+"/"+(String)NTPTime.year()+" ";
            sDate += (String)NTPTime.hour()+":"+(String)NTPTime.minute()+":";
            sDate += (String)NTPTime.second();
            DSPL( dPrompt + "NTP Time : " + sDate );
            _pDisplay->println("NTP Time");
            _pDisplay->println(sDate);
            _pDisplay->display();
            
            if (_rtc.lostPower()){
                RTC_DS3231::adjust( NTPTime );
                DSPL( dPrompt + F("DS3231 set to NTP time due to power lost.") );
                // CRtc::displayTime();
            }
            _pcParam->write2Json( "ntpError", "OFF" );
        } else { 
            DSPL( dPrompt +"NTP ERROR");
            _pcParam->write2Json( "ntpError", "ON" ); }
    }    
}

void CSystem::_oledStartMessagesManager(){
    DEFDPROMPT( "CSystem::init:Stratup Messages" )
    _pDisplay->drawBitmap(0,0, CSystem::logoLab, 128, 64, 1 );
    _pDisplay->display();
    DSPL( dPrompt + F("OLED Logo pause") );
    delay(OLED_LOGO_DISPLAY_TEMPO);
    _pDisplay->clearDisplay();
    _pDisplay->setTextSize(1);
    _pDisplay->setTextColor(WHITE);
    _pDisplay->setCursor(0,0);
    _pDisplay->println(PROVIDER_NAME);
    _pDisplay->println();
    _pDisplay->println(EPS_NAME1);
    _pDisplay->println(EPS_NAME2);
    _pDisplay->println(EPS_NAME3);
    _pDisplay->display();
    DSPL( dPrompt +F("OLED startup message pause") );
    delay(OLED_STARTUP_MESSAGE_TEMPO);
    _pDisplay->clearDisplay();
    _pDisplay->display();

}
