volab/IoT_EPS/_3_software/IoT_EPS/csysstat.h

/**
 @file csysstat.h
 @author J.SORANZO
 @date 24/04/2019
 @copyright 2019 CC0
 @version git versionning
 @brief CCsysStatt class header file
*/

#ifndef CSYSSTAT_H
#define CSYSSTAT_H
#include <FastLED.h>
#include "config_advanced.h"

class sysError {
    public:
        typedef CRGB::HTMLColorCode gColor_t;
        enum  errGravity_t { low, medium, high, fatal };
        sysError(){ _err = false; };
        // sysError( errGravity_t grav ){ _err = false; _gravity = grav; };
        sysError( errGravity_t grav, String s ){ _err = false; _gravity = grav; _errMsg = s; };
        // sysError( errGravity_t grav,  gColor_t c1, gColor_t c2);
        sysError( errGravity_t grav,  gColor_t c1, gColor_t c2, String s);
        void err( bool errorState );
        bool isErr(){ return _err; }
        String getMsg(){ return _errMsg; }
        bool _forceSystemStartOnFatalError; /**< @brief for debug purpose only, prevent system
        to blink big led and stay in this loop indefinitly        */
        errGravity_t getGravity(){ return _gravity; }
        gColor_t getDisplayColor( bool c ){ return (c  ? _displayColor1 : _displayColor2 ); }
        
    private:
        bool _err = false;
        errGravity_t _gravity = low;
        gColor_t _displayColor1 = CRGB::Black;
        gColor_t _displayColor2 = CRGB::Black;
        String _errMsg;
        
};

class CSysStatus {
    public:
        /** 
         @fn CSysStatus::CSysStatus()
         @brief CSysSattus constructor...
         @return no return value and no parameter

        Allow to creat and initialize errors variables
        */
        CSysStatus():
/* Message max lenght 20c for oled display */
              fsErr( sysError::fatal, CRGB::Red, CRGB::Black, "File system error" )
            , nanoErr( sysError::fatal, CRGB::Red, CRGB::Blue, "Nano error" )
            , rtcErr( sysError::fatal, CRGB::Brown, CRGB::Black, "DS3231 error" ) 
            , confFileErr( sysError::fatal, CRGB::Red, CRGB::Yellow, "Config file error" )
            , credFileErr( sysError::medium, "Credential error" )
            , filesErr( sysError::fatal, CRGB::OrangeRed, CRGB::Black, "Needed files error" )
            , plugParamErr( sysError::fatal, CRGB::Red, CRGB::Snow,    "Plug's file error"  )
            , ntpErr( sysError::low, "NTP error")
            , internetErr( sysError::fatal, CRGB::RoyalBlue, CRGB::OrangeRed, "Internet error" )
            , watchdogErr( sysError::medium, CRGB::Snow, CRGB::Black, "watchdog error")
            , wifiSoftApErr(sysError::medium, CRGB::Snow, CRGB::Black, "SoftAp error")
            /** @todo [NECESSARY] creat wifiErr and wifiStaModeErr (choose a color) */
            // what diff between this 2 errors ? fatal or not 
            // wifi station mode is medium error  wifi too 
            // with this 2 error no web browser access i think we should merge
            {
            
        }
        // CSysStatus();
        sysError fsErr;
        sysError nanoErr;
        sysError rtcErr;
        // sysError i2cErr;
        sysError confFileErr; //config4.json gen parma part error
        sysError credFileErr;
        sysError filesErr;
        sysError plugParamErr;
        sysError ntpErr;
        sysError internetErr;
        sysError watchdogErr;
        sysError wifiSoftApErr;
        /** @todo [NECESSARY] creat wifiSoftAPErr and wifiErr don't forget to increase NBR_OF_SYSTEM_ERROR*/
        
        sysError* sysErrorTable[NBR_OF_SYSTEM_ERROR] = { 
                    &fsErr, &nanoErr, &rtcErr, &confFileErr, &credFileErr, &filesErr, &plugParamErr, 
                    &ntpErr, &internetErr, &watchdogErr, &wifiSoftApErr };
        
        bool ntpEnabled = false; //set to true when Station mode is ok
        bool wifiErr = false;
        
        void display();
        
        void initCBITTimer();
        bool isCbitTime();

        /** @brief Return anded global system state */
        bool isSystemok();
        int8_t isThereFatalError(); 
        
        /** @brief  return the number of error for oled display */
        int8_t howManyError();

        String getMsg( int8_t n);

        bool isTimeToSwitchColorLed();
       
    private:
        unsigned long _prevMillisCbit;
        unsigned long _prevMillisForColorLed = 0;
        uint8_t _fatalErrorCpt = 0;
};

extern CSysStatus sysStatus;

#endif
