volab/IoT_EPS/_3_software/IoT_EPS/configParam.h

/**
* @file configParam.h
* @author J.SORANZO
* @date 2018
* @copyright 2018 CC0
* @version 1.0
* @brief header file of the ConfigParam class
*/

#include "IoT_EPS.h"
//#pragma once
#ifndef CONFIGPARAM_H
#define CONFIGPARAM_H


#include "debugSerialPort.h"
#include <IPAddress.h>
// #define CONFIGFILENAME "/config4.json"


class ConfigParam{
    public:

        enum firstBootVal { YES, NO, TRY };
    
        bool ready = false;
        void begin( ); 
        String getWifiMode(){ return _wifimode; }
		void setWifiMode( String mode ){ _wifimode = mode ; }
        String getHostName(){ return _host; }
		static void displayJson( String file = CONFIGFILENAME );
		void displayWifiMode();
        static void displayJsonGeneral();
        
        // static void chgSSID( String value, String key = "ssid" );
        void chgSSID( String value, String key = "ssid" );
        // static void chgWifiPass( String value, String key = "pass" );
        void chgWifiPass( String value, String key = "pass" );
        IPAddress getIPAdd(){ return _addIP; }
        int getNumberOfPlugs(){ return _numberOfPlugs; }
        int getServerPort(){ return _serverPort; }
        long getAllLedsOnTime(){ return _allLedsOnTime; }
        int getLedsLuminosity(){return _ledsGlobalLuminosity; }
        /** DONE read _powerLedEconomyMode parameter in the config file...*/
        bool getPowLedEconomyMode(){ return _powerLedEconomyMode; } 
        firstBootVal getFirstBoot(){ return _firstBoot; }
        void setFirstBoot( firstBootVal val ){ _firstBoot = val; }
        // static void write2Json( String param, String value, String file = CONFIGFILENAME );
        void write2Json( String param, String value, String file = CONFIGFILENAME );
        // static void _write2CredJson( String param, String value );
        unsigned int getSTAMaxRetries(){ return _STAmaxWifiConnectionRetries; }
        String getMacAdd(){ return _macAdd; }
        String getSoftAPMacAdd(){ return _softAPMacAdd; }
        bool getDHCPMode(){ return _DHCPMode; }
        IPAddress getStaIP(){ return _staIP; }
        IPAddress getStaGatewayIP(){ return _staGateway; }
        void creatDefaultJson();
        static String readFromJsonParam( String parameter, String section );
    
    private:
        String _wifimode = "" ; //default value
        String _host= "";
        bool readFromJson();
        IPAddress _addIP; /**< brief warning softAP IP */
        int _numberOfPlugs = 1;
        int _serverPort;
        long _allLedsOnTime;
        bool _powerLedEconomyMode = false;
        //in seconds (not unsigned cause -1 could serve to allways on in future)
        int _ledsGlobalLuminosity;
        firstBootVal _firstBoot;
        unsigned int _STAmaxWifiConnectionRetries = 0 ;
        String _macAdd;
        String _softAPMacAdd;
        bool _DHCPMode;
        IPAddress _staIP;
        IPAddress _staGateway;
        // bool _fileCopy( String from, String to);
        String _emplacement;
        bool _startInApMode;
        bool _jsonWriteRequest = false;

        friend class CJsonIotEps;
        friend class CServerWeb;
        

};

#endif
