volab/IoT_EPS/_3_software/IoT_EPS/CServerWeb.h

/**
 @file CServerWeb.h
 @author J.SORANZO / VoLAB
 @date 15/08/2020
 @copyright 2020 CC0
 @version git versionning
 @brief hearder file of the class CServerWeb web of the project IoT_EPS
*/
#include "IoT_EPS.h"
// #include "CRtc.h"
//#include "cpowerplug.h"

#ifndef CWEBSERVEUR_H
#define CWEBSERVEUR_H


/**
 * @class CServerWeb CServerWeb.h
 * @brief cserverWeb class
 */
class CServerWeb
{
    private:
        /* data */
        CRtc *_pRtc = nullptr;
        ESP8266WebServer *server;
        ConfigParam *_pcParam = nullptr;
        int mainPowerSwitchState = 0;
        CPowerPlug *_pPlugs;
        ESP8266WiFiClass *_pWifiConnection; //only for buildWifiMacaddress method
        bool *_pRestartTempoLed;
        bool handleFileRead(String path);
        String getContentType(String filename);
        void handleSoftAPIndex();
        void notFoundHandler();
        // void handleFileList();
        void handleHelp();
        // void handleEdit();
        // void handleFileCreate();
        void htmlOkResponse();
        File _fsUploadFile; // cette variable doit être globale
        //la fonction l'utilise plusieurs fois - ie lors de plusieurs appels pour 1 fichier
        //eventuellement pourrait être static    
        // void handleFileUpload();
        // void handleFileDelete();
        void handleIndex();
        void handelIOTESPConfPage();
        void handleIOTESPConfiguration();
        void handleNewCred();
        void firstBootHtmlForm();
        void handleFirstBoot();
        String buildMacAddName( String prefix);

    public : 
        // CServerWeb(/* args */);
        // ~CServerWeb();
        void init( CRtc * rtc, ConfigParam *cparam, CPowerPlug *plugs
                    , bool *restartTempoLed, ESP8266WiFiClass *pWifiCon );
        void setMPSstVar( int mainPowerSwitchStateVal ){mainPowerSwitchState = mainPowerSwitchStateVal;}
        // void displayTime();
        void serviceClient();
        void handlePlugOnOff(); //29/08/2020 : why public ?
        static String extractParamFromHtmlReq( String allRecParam, String param );
        //static and public for CPowerPlug usage

};

#endif
