volab/IoT_EPS/_3_software/IoT_EPS/cnano.cpp

/**
 @file cnano.cpp
 @author J.SORANZO
 @date 25/01/2019
 @copyright 2018 CC0
 @version git versionning
 @brief Implémentation file of CNano class
*/

#include "cnano.h"

bool CNano::_initDone = false;
CNanoI2CIOExpander CNano::_nano;

void CNano::init(){
    /** @todo [OPTION] take into account initOk of CNanoI2CIOExpander class */
    _initDone = true;
    _nano.begin();
}
