volab/IoT_EPS/_3_software/pythonTools/pyIoTEPS_test/sources/modulesUI/GuiFrameDisplay.py

import tkinter as tk
from tkinter import ttk

# import GuiFrameMag as FMag
# import GuiFrameBaro as FBaro
# import GuiFramePitot as FPit
# import GuiFrameTlm as FTlm
# import GuiFrameAlim as FAlimzTxtHight

import os
import sys
SCRIPT_DIR = os.path.dirname(os.path.abspath(__file__))
sys.path.insert(0,os.path.dirname(SCRIPT_DIR))
import modulesUI.guiPlugs as plug



     

class GuiFrameDisplay(tk.Frame):

    def __init__(self, master, genPad, fenHeight, ztxHeigh, **kwargs):
        self.GEN_PADDING = genPad
        self.FEN_HAUTEUR = fenHeight
        self.ZONE_DE_TEXT_HAUTEUR = ztxHeigh
    
        tk.Frame.__init__(self, master, height=self.FEN_HAUTEUR ,  width=850 , relief=tk.GROOVE, bg="gray", bd=5, class_='CframeOfContrl', **kwargs)
        self.grid(row=1, column=2, padx=self.GEN_PADDING, pady=self.GEN_PADDING)


        self.msgZone=tk.Text(self, bd=5, padx=genPad , pady=genPad , 
            relief=tk.GROOVE, width=100, height= self.ZONE_DE_TEXT_HAUTEUR)
        self.msgZone.grid(row=1, column=1, padx=genPad , pady=genPad, sticky=tk.NW, columnspan=2)

        # self.msgZone.insert(tk.END, "Texte initial")
        s=tk.Scrollbar(self)
        s.grid(row=1, column=3, sticky=tk.N+tk.S)
        s.config(command=self.msgZone.yview)
        self.msgZone.config(yscrollcommand=s.set)

        self.clearBtn = tk.Button( self, text='CLEAR', command=self.clearCmd )  
        self.clearBtn.grid(row=2,column=1, 
                    padx=GEN_PADDING, pady=GEN_PADDING, sticky=tk.N+tk.W)  

        # self.dataBaroFrame = FBaro.GuiFrameBaro( self, 2, 1, self.GEN_PADDING)
        self.redPlug = plug.GuiPlugs(self, GEN_PADDING, "red")
        self.redPlug.grid(row = 3, column = 1, columnspan=2, sticky=tk.NW)

        self.greenPlug = plug.GuiPlugs(self, GEN_PADDING, "green")
        self.greenPlug.grid(row = 4, column = 1, columnspan=2, sticky=tk.NW)

        self.bluePlug = plug.GuiPlugs(self, GEN_PADDING, "blue")
        self.bluePlug.grid(row = 5, column = 1, columnspan=2, sticky=tk.NW)

        self.yellowPlug = plug.GuiPlugs(self, GEN_PADDING, "yellow")
        self.yellowPlug.grid(row = 6, column = 1, columnspan=2, sticky=tk.NW)

    # def updateDataCapteur(self, trameDecoupee ):
    #     self.dataBaroFrame.displayDataCapteur_O( trameDecoupee )

    def clearCmd(self):
        self.msgZone.delete('1.0',tk.END)


import os
import sys
SCRIPT_DIR = os.path.dirname(os.path.abspath(__file__))
sys.path.insert(0,os.path.dirname(SCRIPT_DIR))
from constantes import GEN_PADDING, FEN_HAUTEUR, ZONE_DE_TEXTE_HAUTEUR

def main():
    print("*"*80)
    print('Test du programme :' + os.path.basename(__file__) )
    print("ouvre un fenêtre TK inter")
    root = tk.Tk()
    frameDisplay = GuiFrameDisplay(root, GEN_PADDING, FEN_HAUTEUR, ZONE_DE_TEXTE_HAUTEUR)
    frameDisplay.grid_propagate(0)
    root.mainloop()

if __name__ == '__main__':
    main()
    
